ahmadmadyy/Bicopter-Balancing/Open Loop Tests/Image Tasks/Darkening.jpg

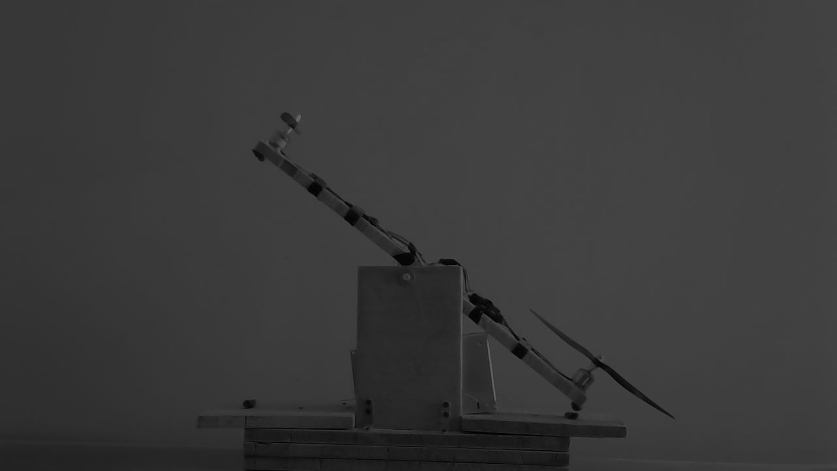
Open Loop Tests/Image Tasks/Darkening.jpg
