ahmadmadyy/Bicopter-Balancing/Open Loop Tests/Image Tasks/Darkening.png

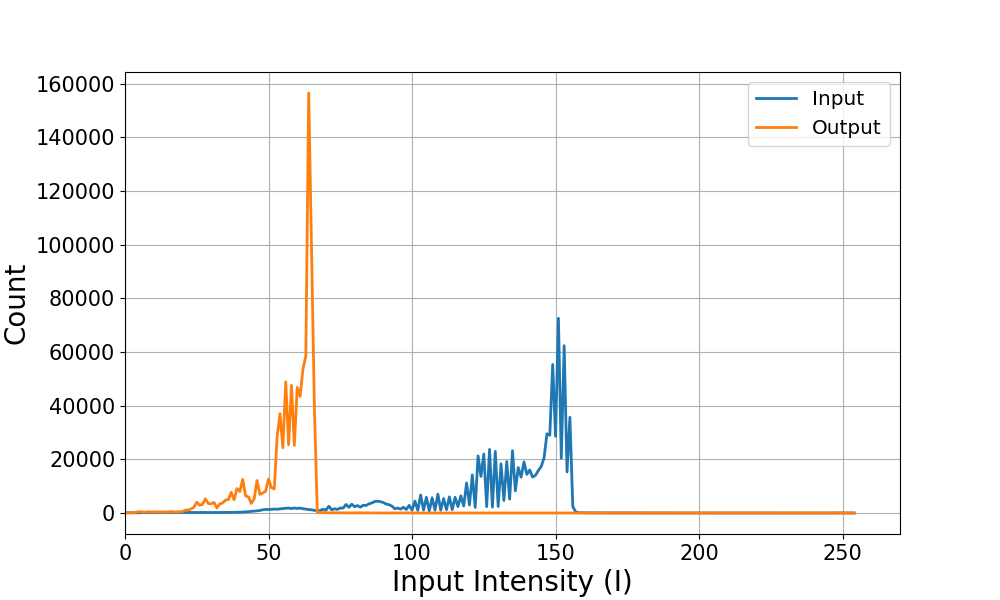
Open Loop Tests/Image Tasks/Darkening.png
