ahmadmadyy/Bicopter-Balancing/Open Loop Tests/Image Tasks/GRAY.jpg

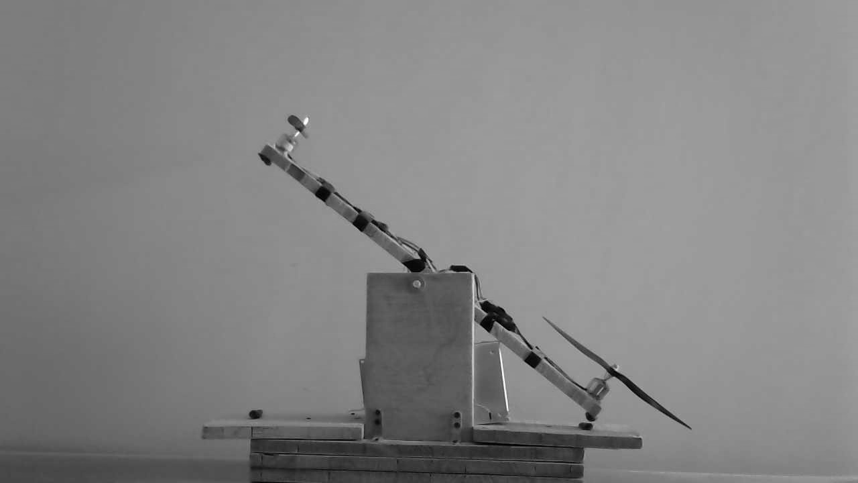
Open Loop Tests/Image Tasks/GRAY.jpg
