ahmadmadyy/Bicopter-Balancing/Open Loop Tests/Image Tasks/GRAYHIST.png.png

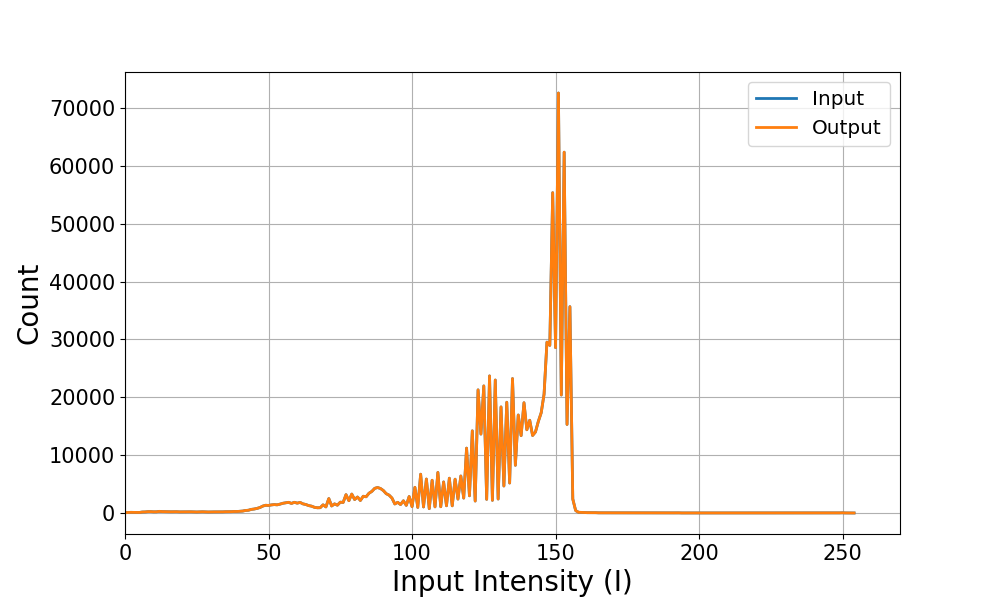
Open Loop Tests/Image Tasks/GRAYHIST.png.png
