ahmadmadyy/Bicopter-Balancing/Open Loop Tests/Image Tasks/Highcontrast.jpg

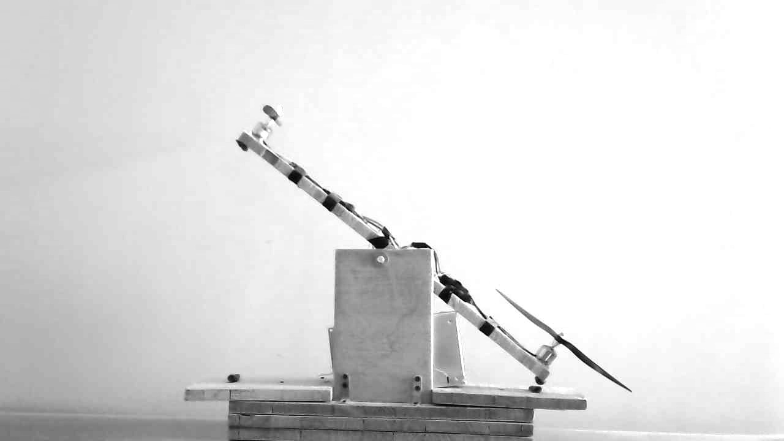
Open Loop Tests/Image Tasks/Highcontrast.jpg
