ahmadmadyy/Bicopter-Balancing/Open Loop Tests/Image Tasks/HighContrastHist.png

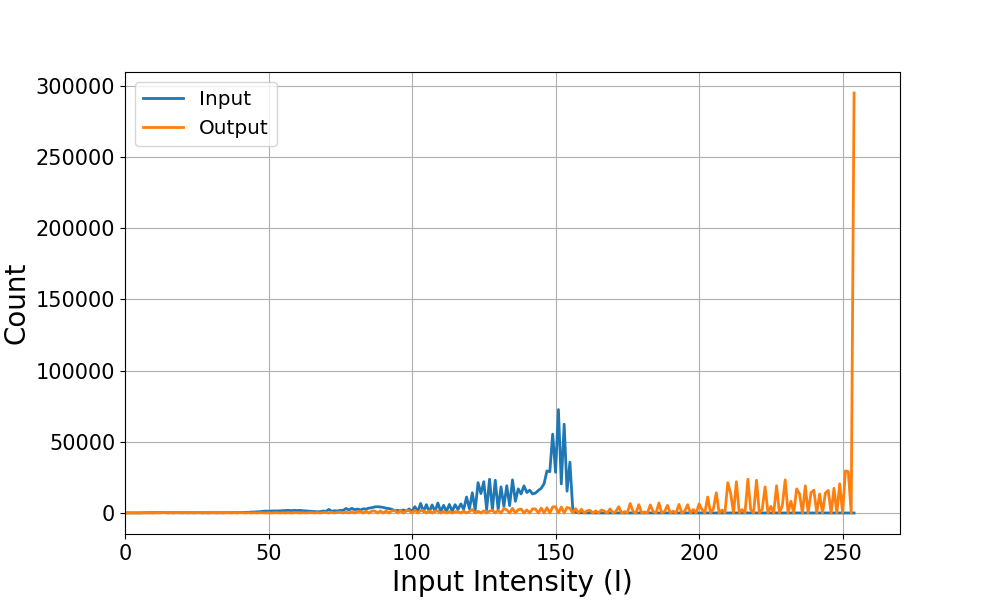
Open Loop Tests/Image Tasks/HighContrastHist.png
