ahmadmadyy/Bicopter-Balancing/Open Loop Tests/Image Tasks/LAB.jpg

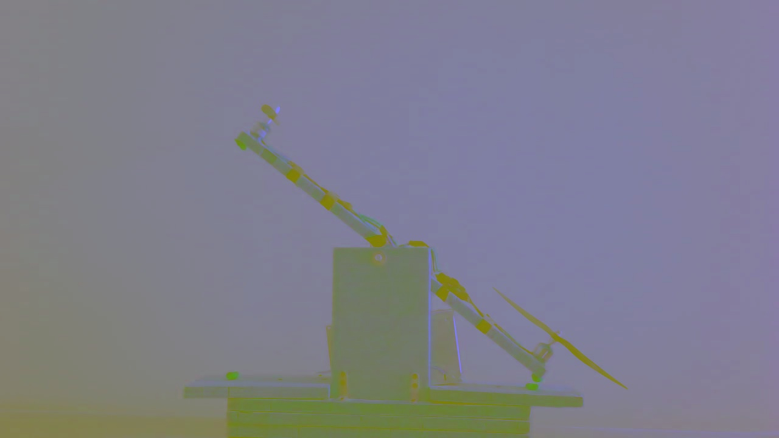
Open Loop Tests/Image Tasks/LAB.jpg
