ahmadmadyy/Bicopter-Balancing/Open Loop Tests/Image Tasks/Scaling.jpg

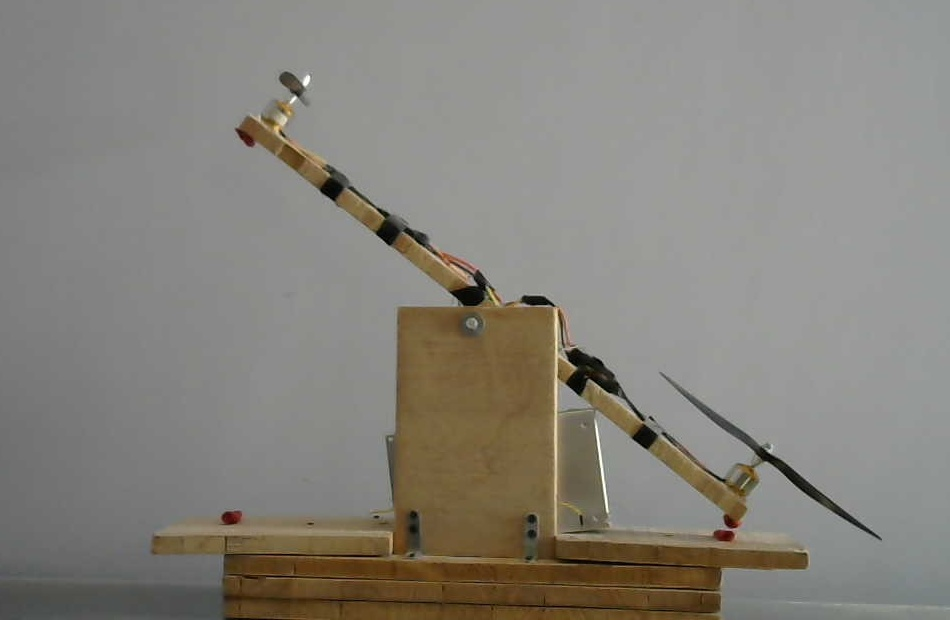
Open Loop Tests/Image Tasks/Scaling.jpg
