ahmadmadyy/Bicopter-Balancing/Open Loop Tests/Image Tasks/Translation.jpg

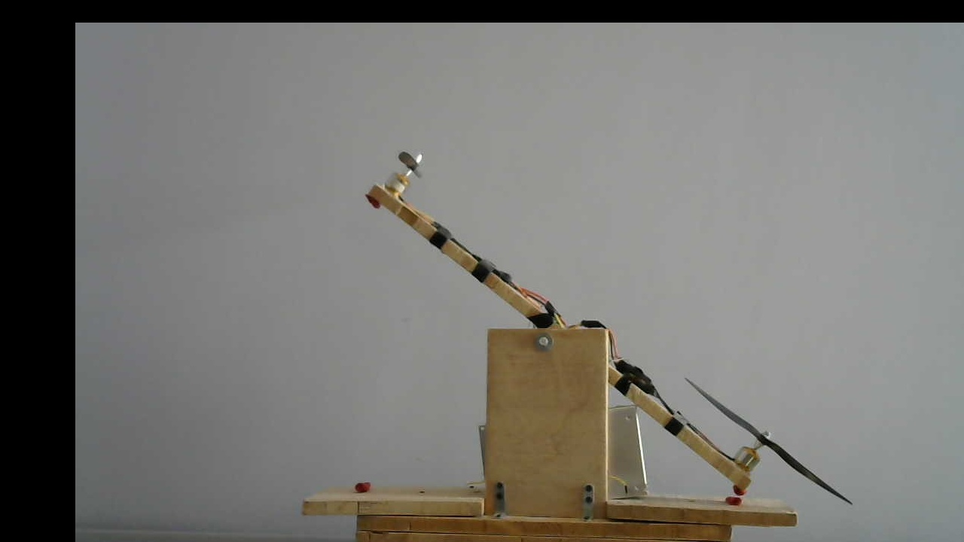
Open Loop Tests/Image Tasks/Translation.jpg
