ahmadmadyy/Bicopter-Balancing/Open Loop Tests/Pics/Solid.jpg

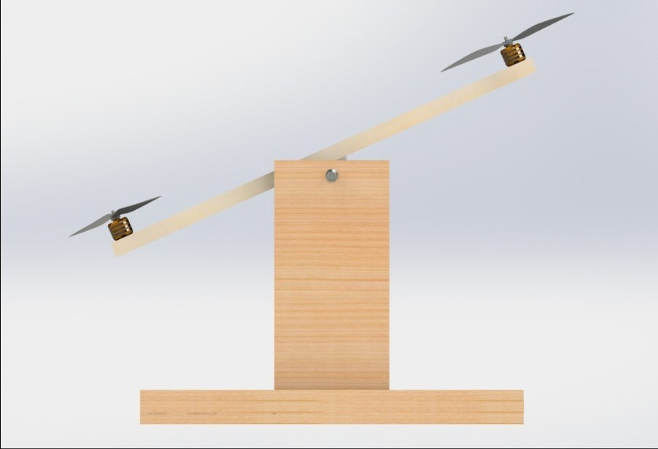
Open Loop Tests/Pics/Solid.jpg
