ahmadmadyy/Bicopter-Balancing/Open Loop Tests/Tests on Camera and PC/Images/LaplacianEdgeDetection.jpg

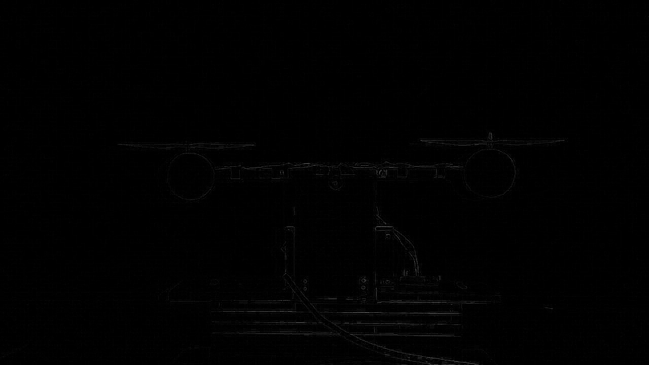
Open Loop Tests/Tests on Camera and PC/Images/LaplacianEdgeDetection.jpg
