ahmadmadyy/Bicopter-Balancing/Open Loop Tests/Tests on Camera and PC/Images/SobelEdgeDetection.jpg

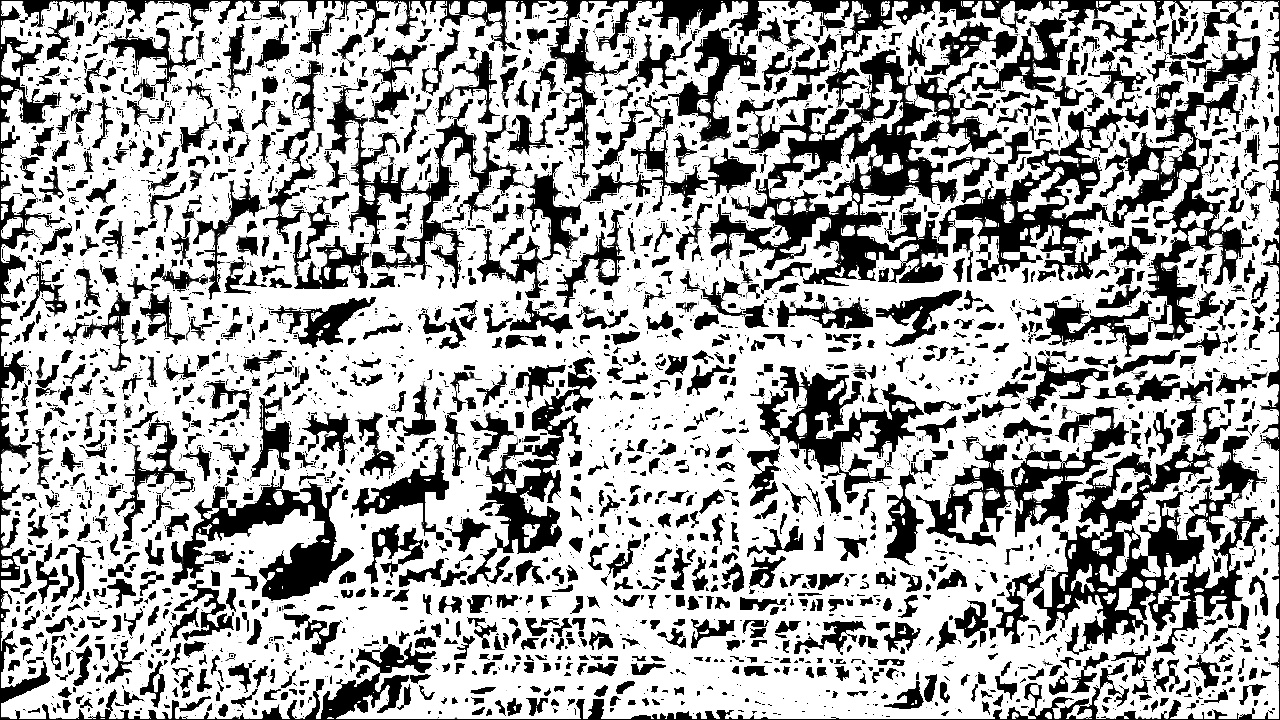
Open Loop Tests/Tests on Camera and PC/Images/SobelEdgeDetection.jpg
