ahmadmadyy/Bicopter-Balancing/Open Loop Tests/Tests on Camera and PC/Images/SobelxEdgeDetection.jpg

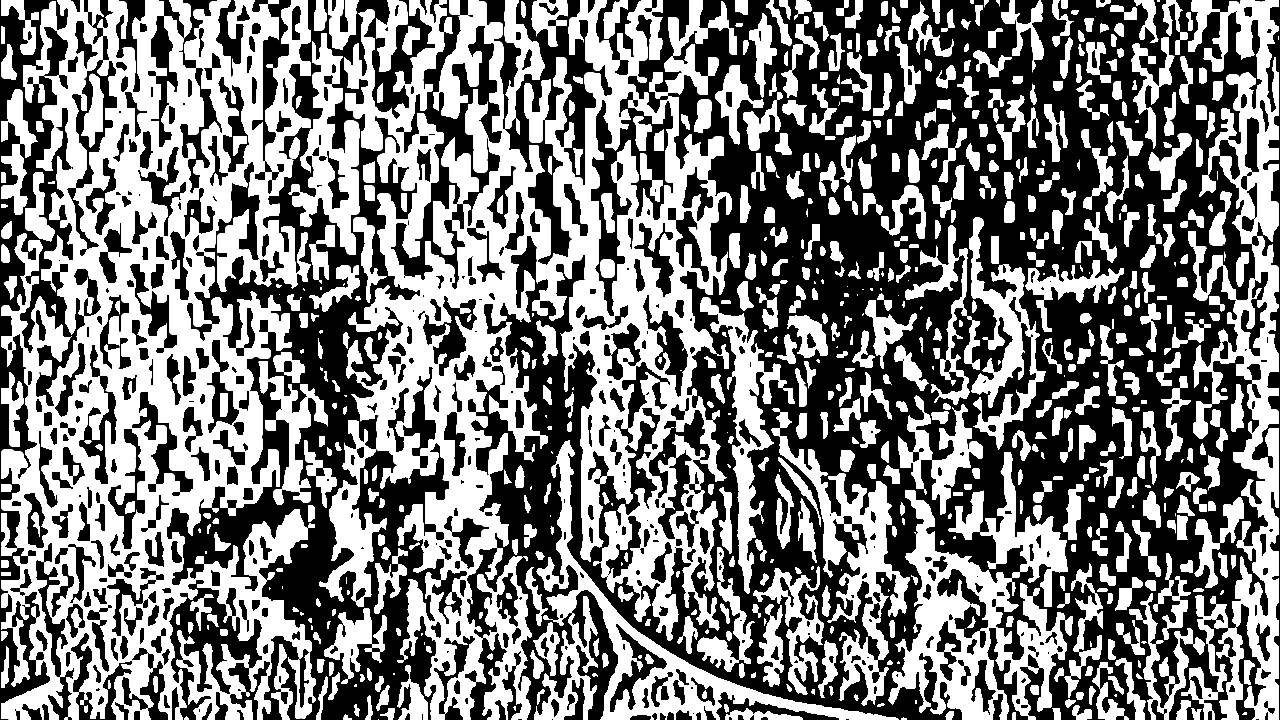
Open Loop Tests/Tests on Camera and PC/Images/SobelxEdgeDetection.jpg
