ahmadmadyy/Bicopter-Balancing/Open Loop Tests/Tests on Camera and PC/Images/SobelyEdgeDetection.jpg

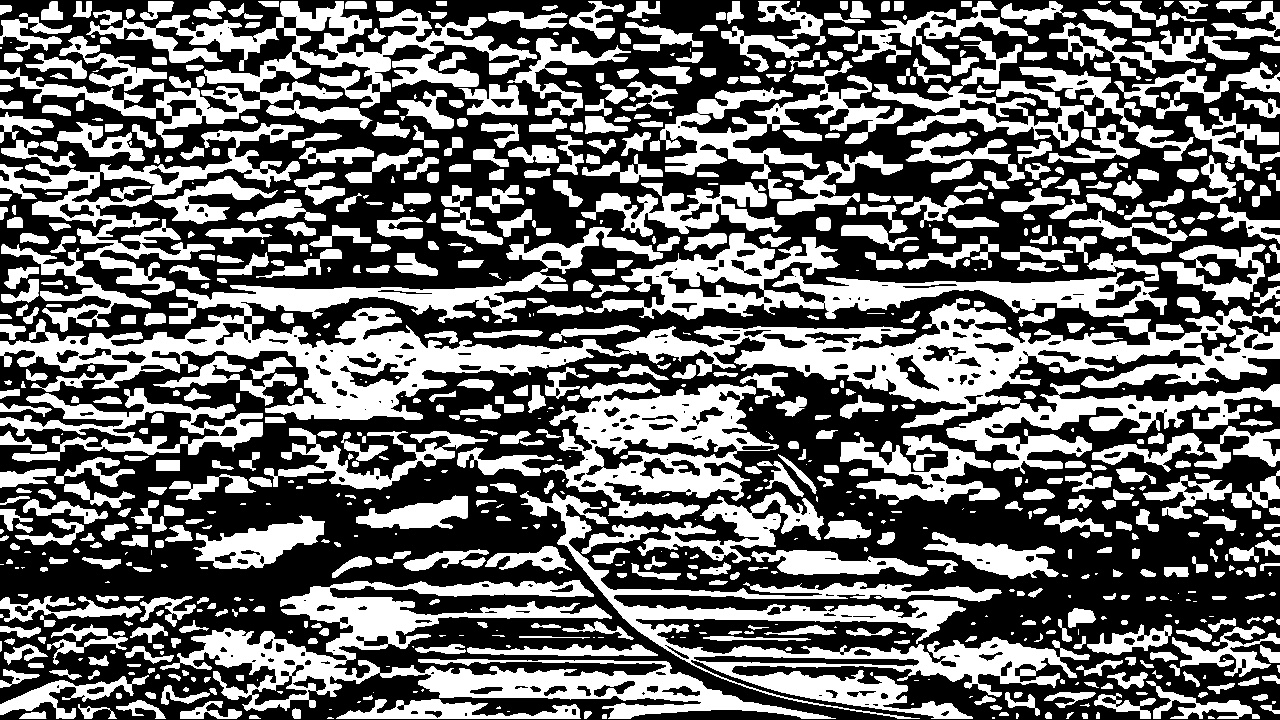
Open Loop Tests/Tests on Camera and PC/Images/SobelyEdgeDetection.jpg
